adamkral20-svg/DIY-amplifier/assets/Layer 2.png

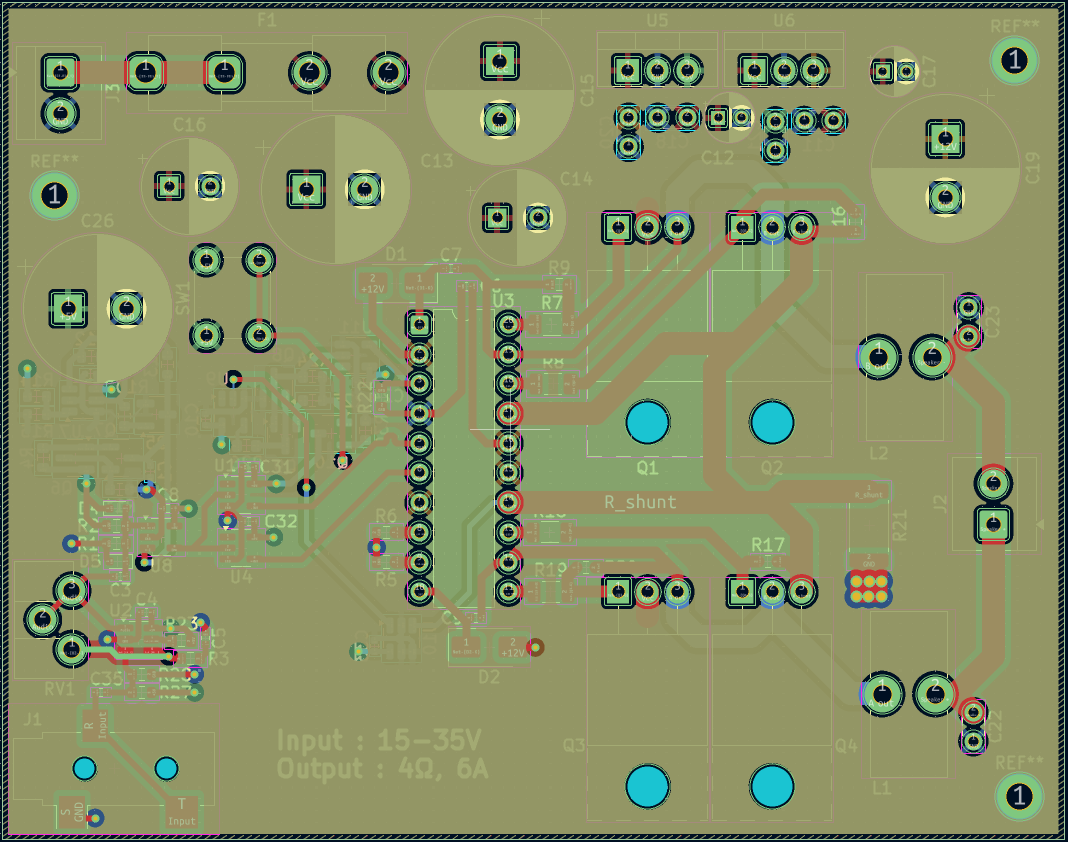
assets/Layer 2.png
