adamkral20-svg/DIY-amplifier/assets/Layer 3.png

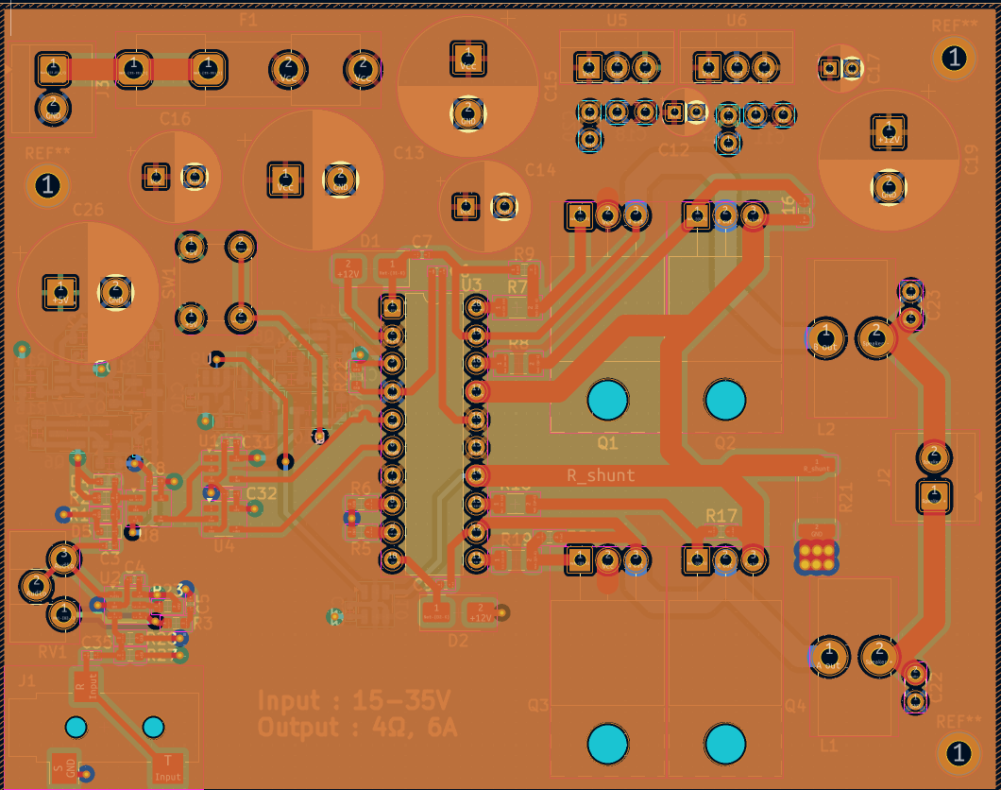
assets/Layer 3.png
