adamkral20-svg/DIY-amplifier/assets/mosfets.png

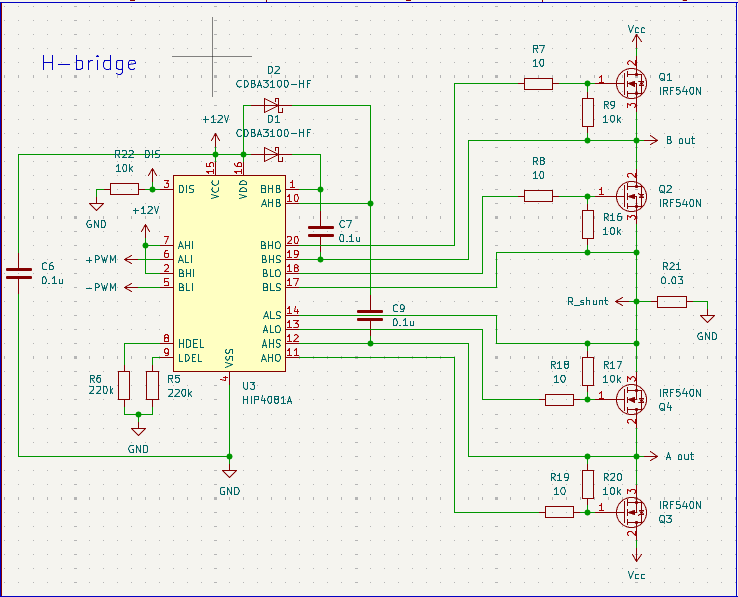
assets/mosfets.png
