adamkral20-svg/DIY-amplifier/assets/OCP.png

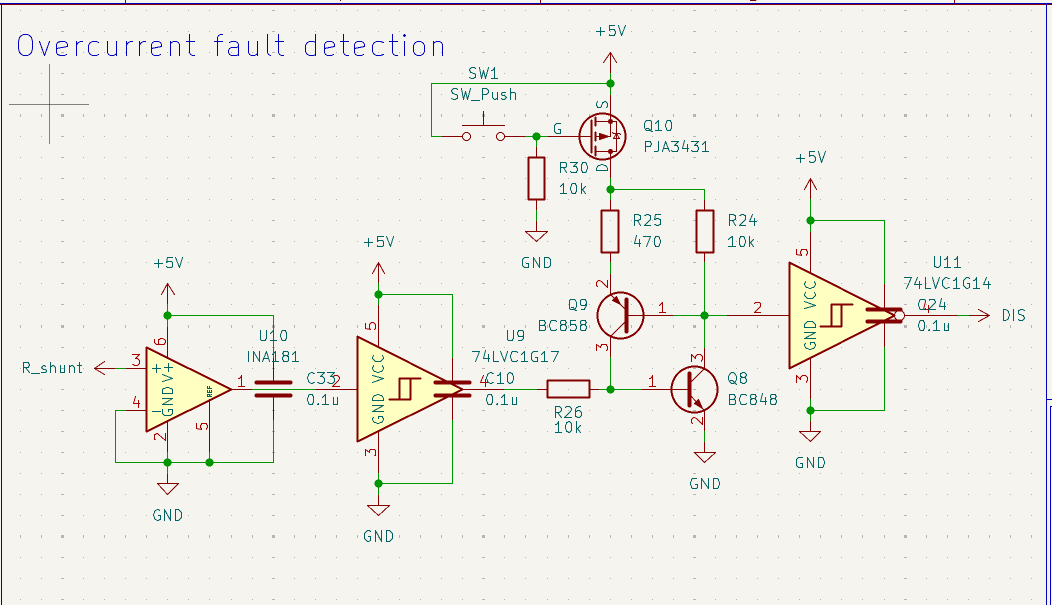
assets/OCP.png
