adamkral20-svg/DIY-amplifier/assets/SineLab_Saw.png

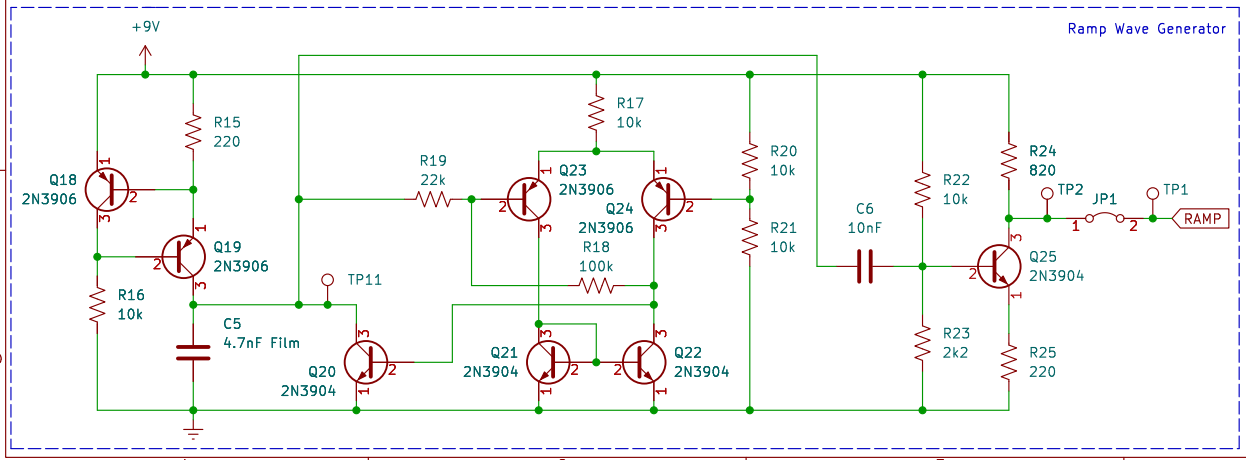
assets/SineLab_Saw.png
